lucullusTheOnly/OpenLaserTag/Wiki/LaserTag_IR_Modulation.png

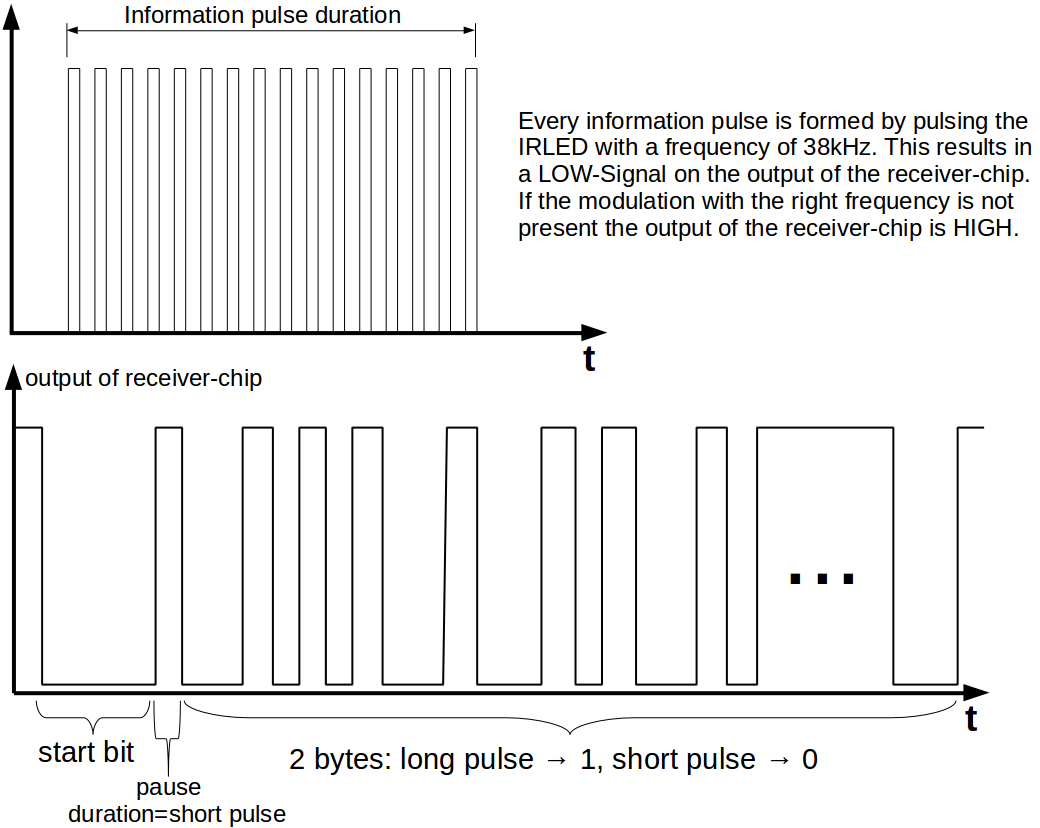
Wiki/LaserTag_IR_Modulation.png
