lucullusTheOnly/OpenLaserTag/Wiki/LaserTag_IR_protocol.png

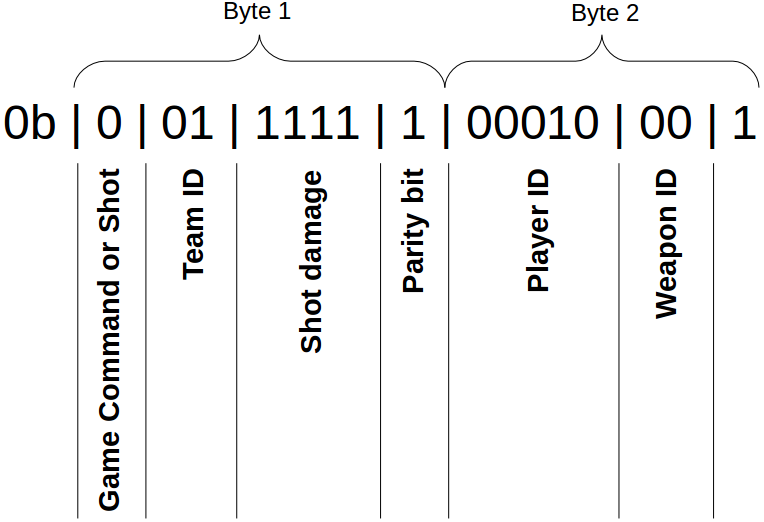
Wiki/LaserTag_IR_protocol.png
